jcorbin/gridfinity-risers/hex_cup_models/hex_cup_2x2x4.stl

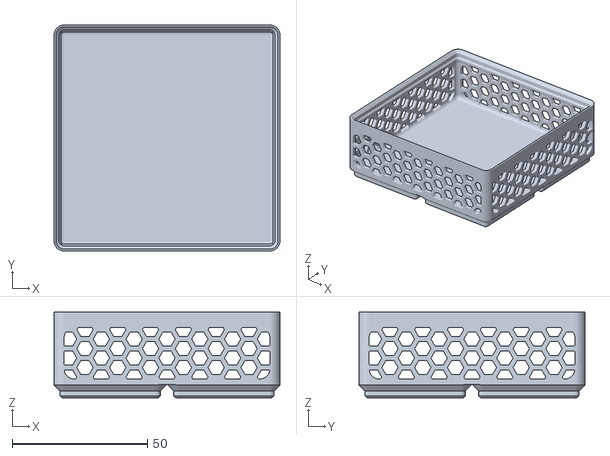
[picture p22: CAD file, 2023-05-15]
hex_cup_models/hex_cup_2x2x4.stl
83.5 x 83.5 x 31.8
