jcorbin/gridfinity-risers/riser_models/tunnel_tower_2x1x18.stl

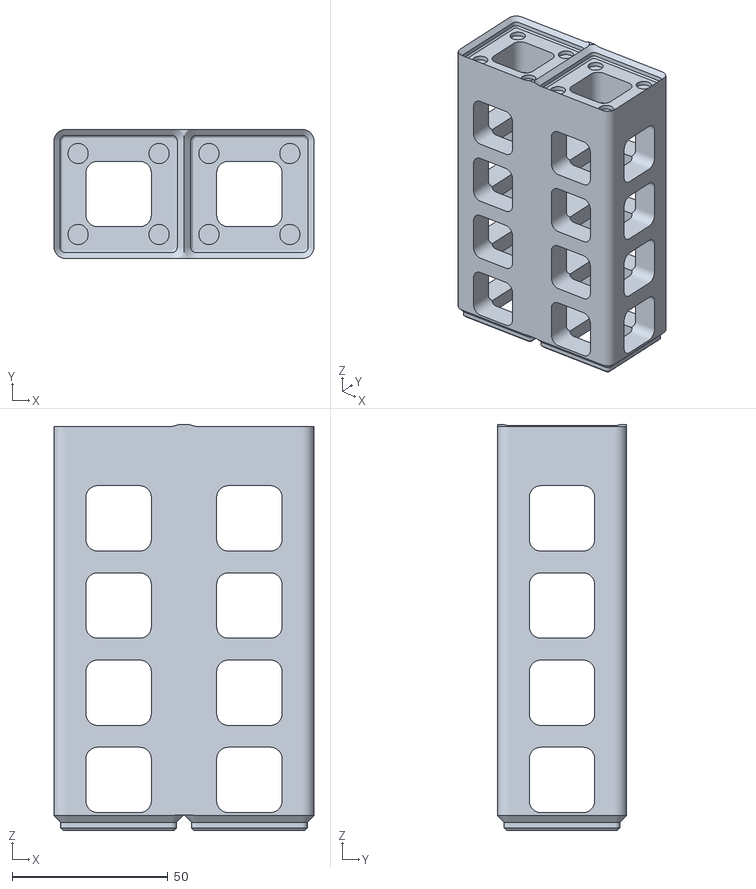
[picture p23: CAD file, 2023-05-11]
riser_models/tunnel_tower_2x1x18.stl
83.5 x 41.5 x 130.4
