jcorbin/gridfinity-risers/hex_cup_models/hex_cup_3x3x6.stl

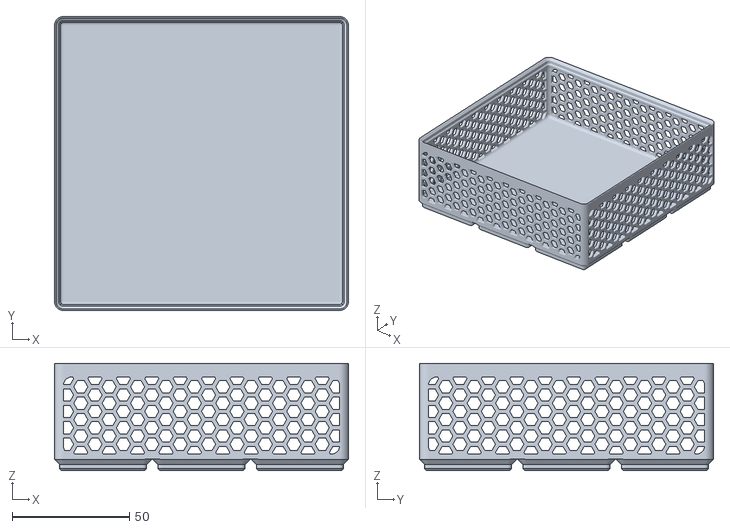
[picture p26: CAD file, 2023-05-15]
hex_cup_models/hex_cup_3x3x6.stl
125.5 x 125.5 x 45.8
