jcorbin/gridfinity-risers/riser_models/tunnel_riser_2x1x4.stl

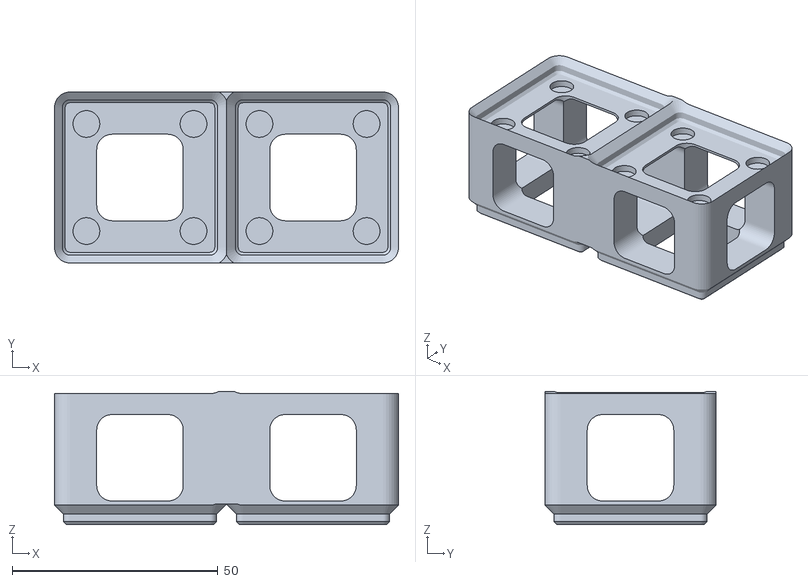
[picture p27: CAD file, 2023-05-11]
riser_models/tunnel_riser_2x1x4.stl
83.5 x 41.5 x 32.4
