jcorbin/gridfinity-risers/hex_cup_models/hex_cup_1x1x6_nolip.stl

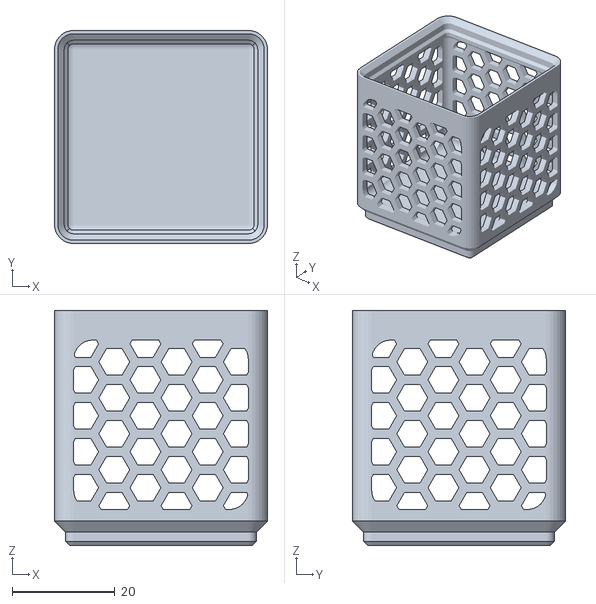
[picture p28: CAD file, 2023-05-15]
hex_cup_models/hex_cup_1x1x6_nolip.stl
41.5 x 41.5 x 45.8
