jcorbin/gridfinity-risers/riser_models/tunnel_tower_2x2x8.stl

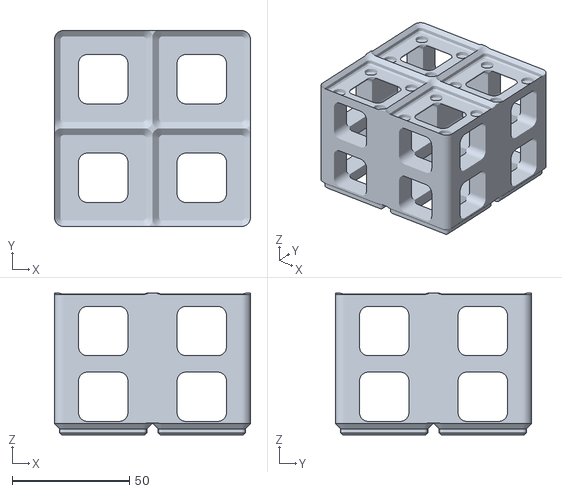
[picture p29: CAD file, 2023-05-11]
riser_models/tunnel_tower_2x2x8.stl
83.5 x 83.5 x 60.4
