jcorbin/gridfinity-risers/riser_models/tunnel_tower_2x2x16.stl

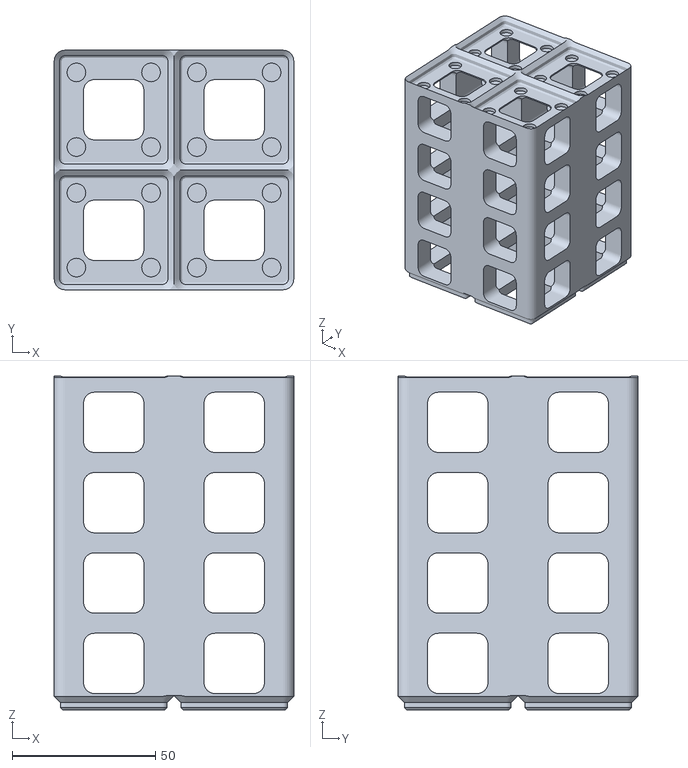
[picture p30: CAD file, 2023-05-11]
riser_models/tunnel_tower_2x2x16.stl
83.5 x 83.5 x 116.4
