jcorbin/gridfinity-risers/hex_cup_models/hex_cup_3x3x4.stl

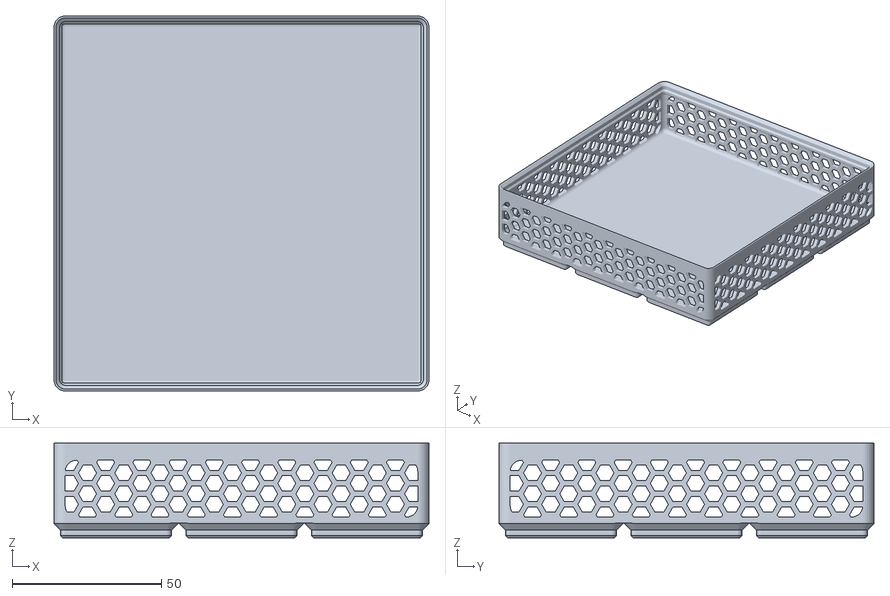
[picture p31: CAD file, 2023-05-15]
hex_cup_models/hex_cup_3x3x4.stl
125.5 x 125.5 x 31.8
