jcorbin/gridfinity-risers/riser_models/tunnel_tower_1x1x18.stl

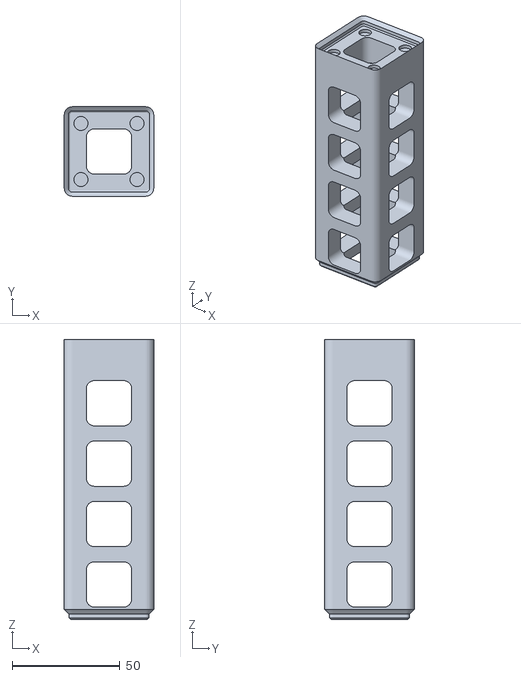
[picture p32: CAD file, 2023-05-11]
riser_models/tunnel_tower_1x1x18.stl
41.5 x 41.5 x 129.8
