jcorbin/gridfinity-risers/riser_models/tunnel_riser_4x2x4.stl

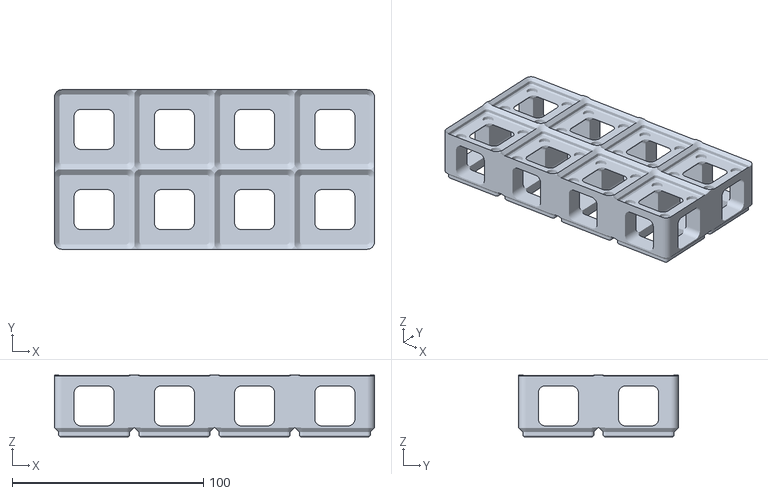
[picture p33: CAD file, 2023-05-11]
riser_models/tunnel_riser_4x2x4.stl
167.5 x 83.5 x 32.4
