jcorbin/gridfinity-risers/riser_models/tunnel_riser_3x2x4.stl

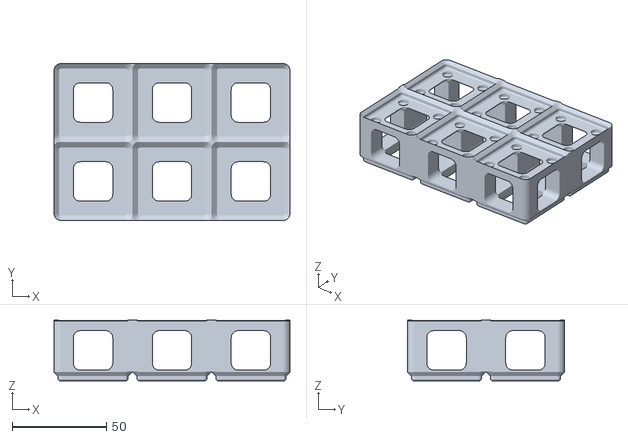
[picture p35: CAD file, 2023-05-11]
riser_models/tunnel_riser_3x2x4.stl
125.5 x 83.5 x 32.4
