jcorbin/gridfinity-risers/hex_cup_models/hex_cup_1x1x12_nolip.stl

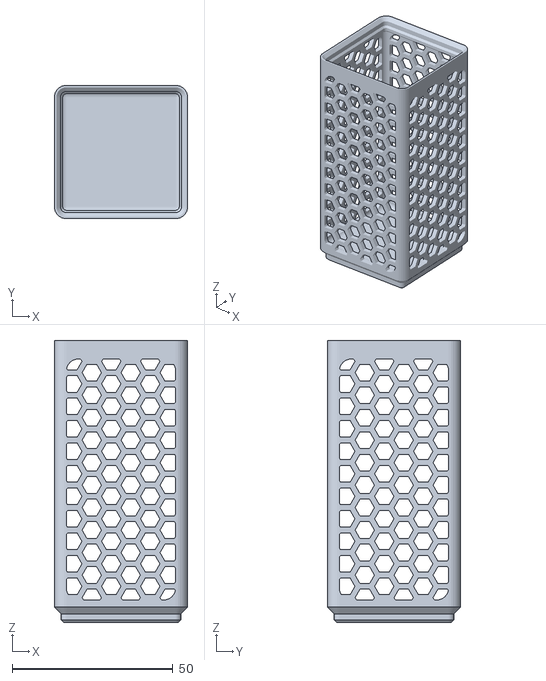
[picture p37: CAD file, 2023-05-15]
hex_cup_models/hex_cup_1x1x12_nolip.stl
41.5 x 41.5 x 87.8
