jcorbin/gridfinity-risers/riser_models/tunnel_tower_2x2x18.stl

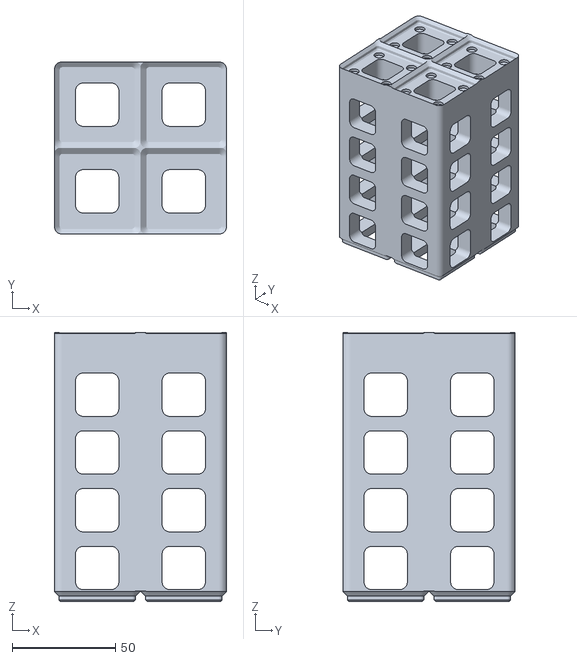
[picture p38: CAD file, 2023-05-11]
riser_models/tunnel_tower_2x2x18.stl
83.5 x 83.5 x 130.4
