jcorbin/gridfinity-risers/riser_models/tunnel_tower_2x1x16.stl

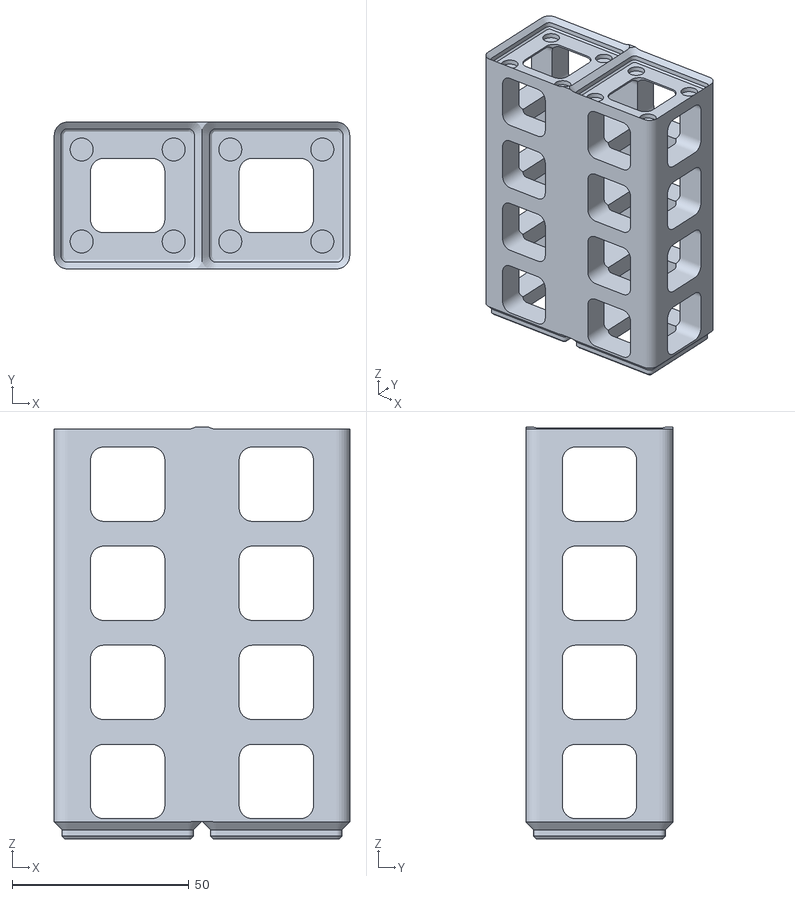
[picture p39: CAD file, 2023-05-11]
riser_models/tunnel_tower_2x1x16.stl
83.5 x 41.5 x 116.4
