jcorbin/gridfinity-risers/riser_models/tunnel_tower_1x1x8.stl

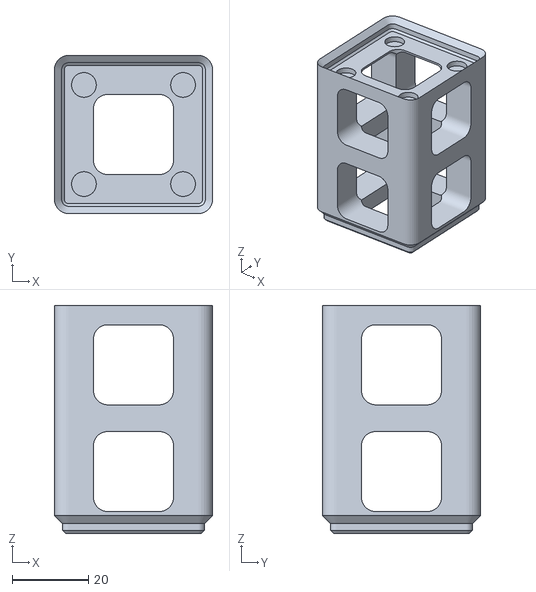
[picture p41: CAD file, 2023-05-11]
riser_models/tunnel_tower_1x1x8.stl
41.5 x 41.5 x 59.8
