jcorbin/gridfinity-risers/riser_models/tunnel_tower_2x2x20.stl

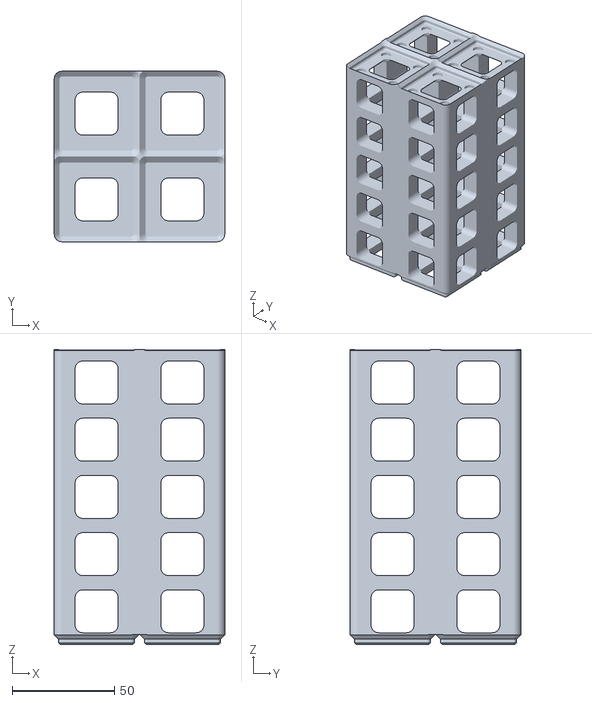
[picture p43: CAD file, 2023-05-11]
riser_models/tunnel_tower_2x2x20.stl
83.5 x 83.5 x 144.4
