jcorbin/gridfinity-risers/riser_models/tunnel_riser_2x2x4.stl

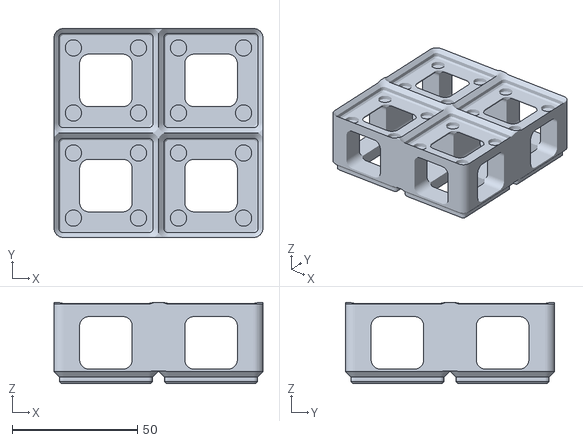
[picture p44: CAD file, 2023-05-11]
riser_models/tunnel_riser_2x2x4.stl
83.5 x 83.5 x 32.4
