jcorbin/gridfinity-risers/hex_cup_models/hex_cup_2x2x12.stl

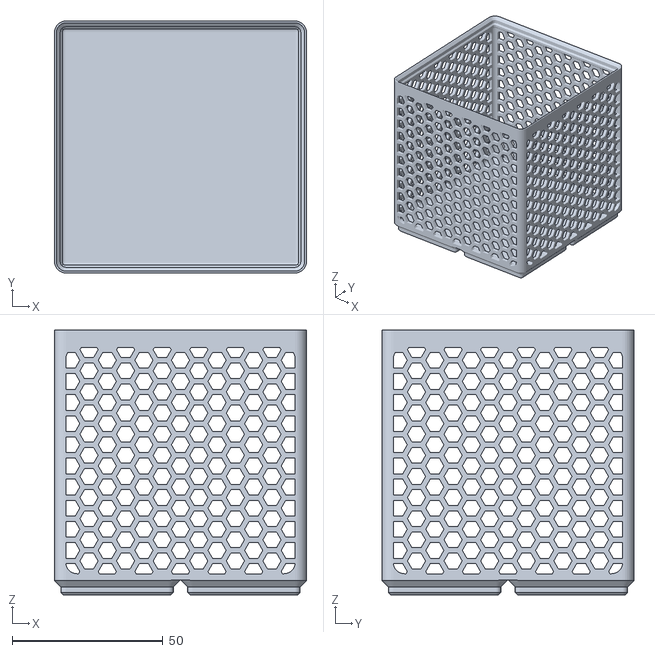
[picture p45: CAD file, 2023-05-15]
hex_cup_models/hex_cup_2x2x12.stl
83.5 x 83.5 x 87.8
