jcorbin/gridfinity-risers/riser_models/tunnel_riser_4x1x4.stl

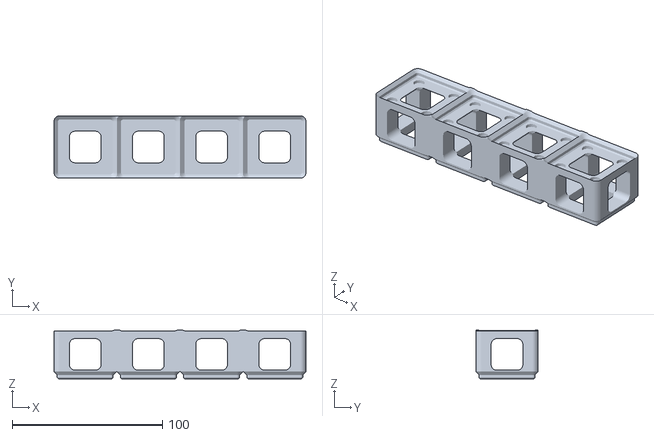
[picture p46: CAD file, 2023-05-11]
riser_models/tunnel_riser_4x1x4.stl
167.5 x 41.5 x 32.4
