jcorbin/gridfinity-risers/riser_models/tunnel_riser_1x1x4.stl

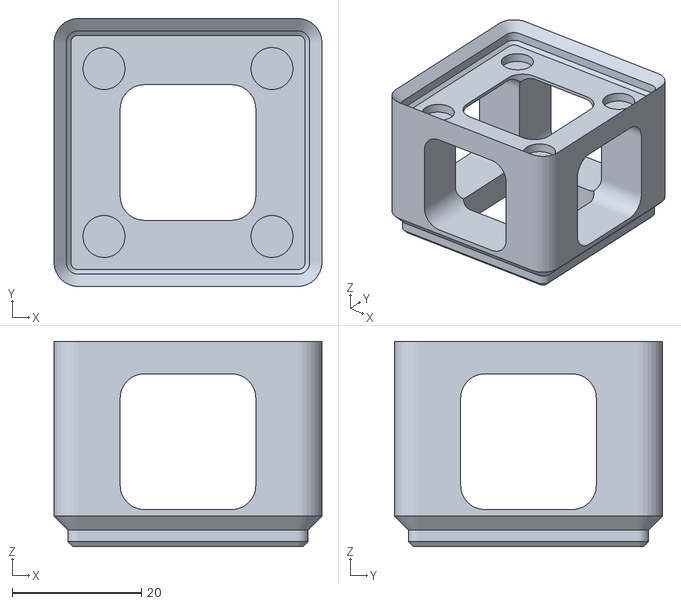
[picture p47: CAD file, 2023-05-11]
riser_models/tunnel_riser_1x1x4.stl
41.5 x 41.5 x 31.8
