jcorbin/gridfinity-risers/riser_models/tunnel_tower_1x1x20.stl

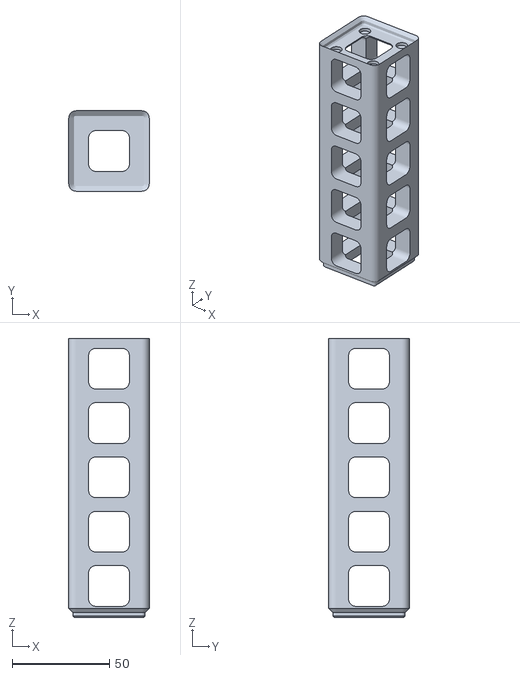
[picture p48: CAD file, 2023-05-11]
riser_models/tunnel_tower_1x1x20.stl
41.5 x 41.5 x 143.8
