jcorbin/gridfinity-risers/hex_cup_models/hex_cup_1x2x6.stl

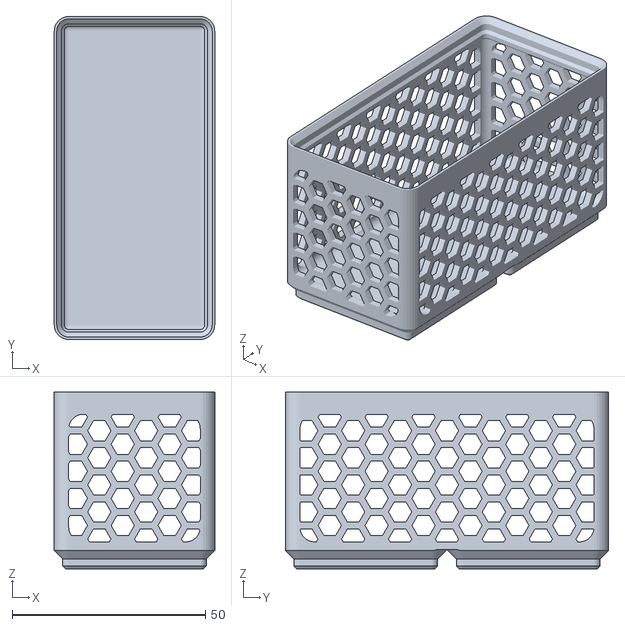
[picture p49: CAD file, 2023-05-15]
hex_cup_models/hex_cup_1x2x6.stl
41.5 x 83.5 x 45.8
