jcorbin/gridfinity-risers/hex_cup_models/hex_cup_2x3x12.stl

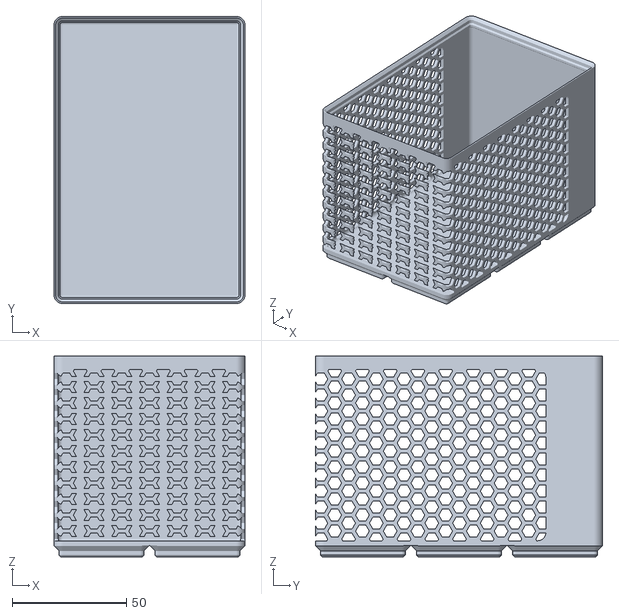
[picture p50: CAD file, 2023-05-14]
hex_cup_models/hex_cup_2x3x12.stl
83.5 x 125.5 x 87.8
