jcorbin/gridfinity-risers/hex_cup_models/hex_cup_3x2x12.stl

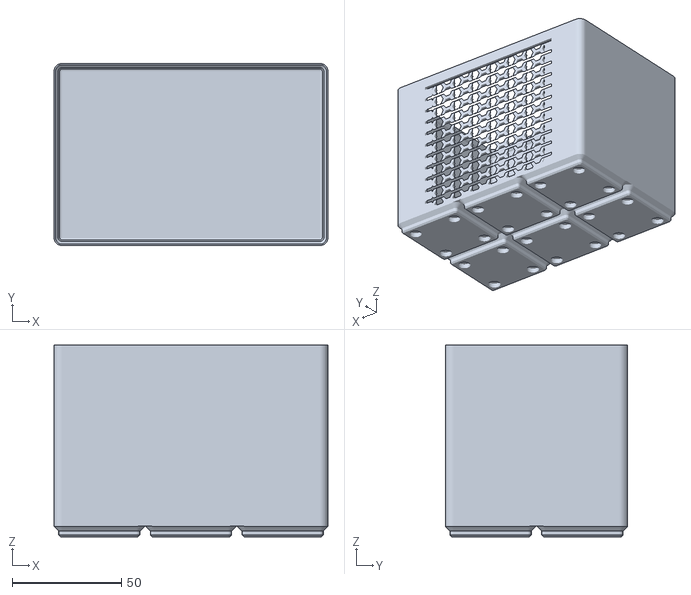
[picture p51: CAD file, 2023-05-14]
hex_cup_models/hex_cup_3x2x12.stl
125.5 x 83.5 x 87.8
